Nurgak/Snail-Mail-Notifier/Images/emitter_etched.jpg

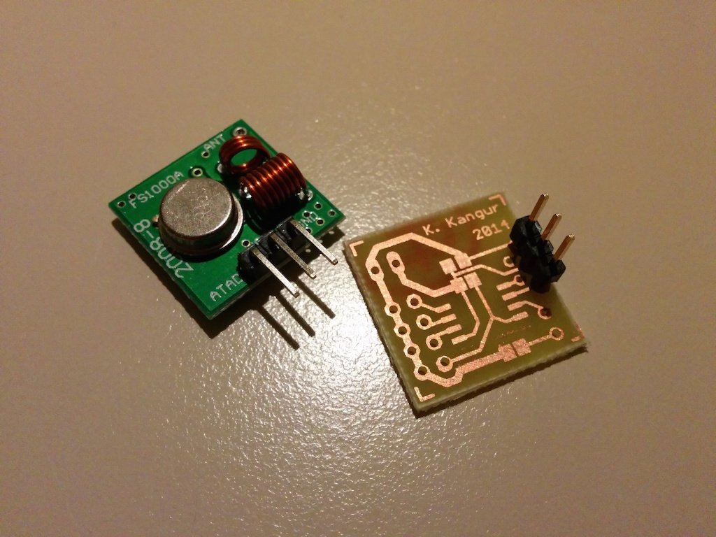
Images/emitter_etched.jpg
