Nurgak/Snail-Mail-Notifier/Images/emitter_programming.jpg

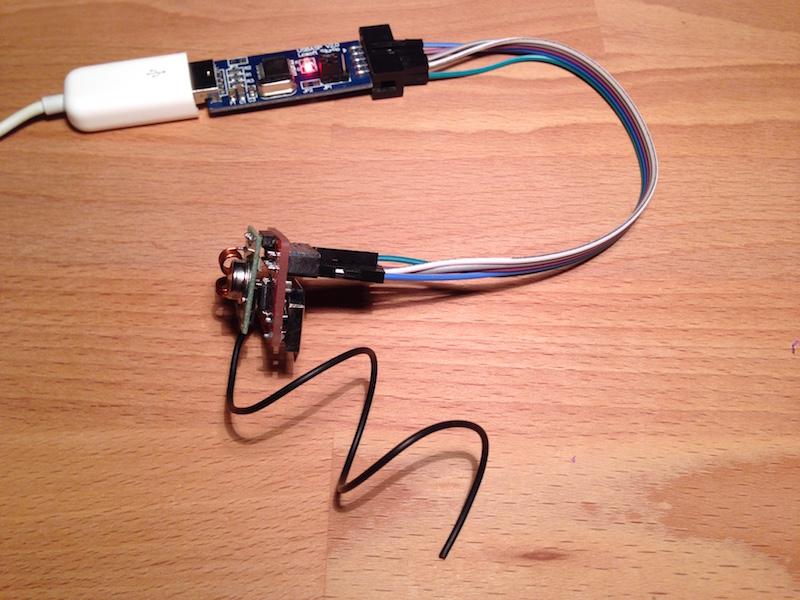
Images/emitter_programming.jpg
