Nurgak/Snail-Mail-Notifier/Images/media-20150113.jpg

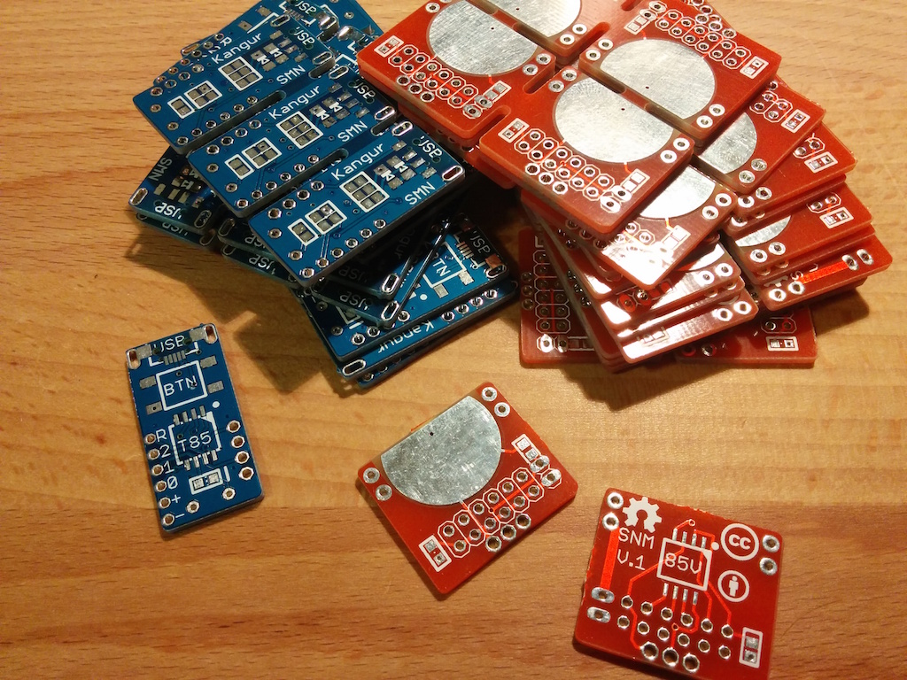
Images/media-20150113.jpg
