Nurgak/Snail-Mail-Notifier/Images/receiver.jpg

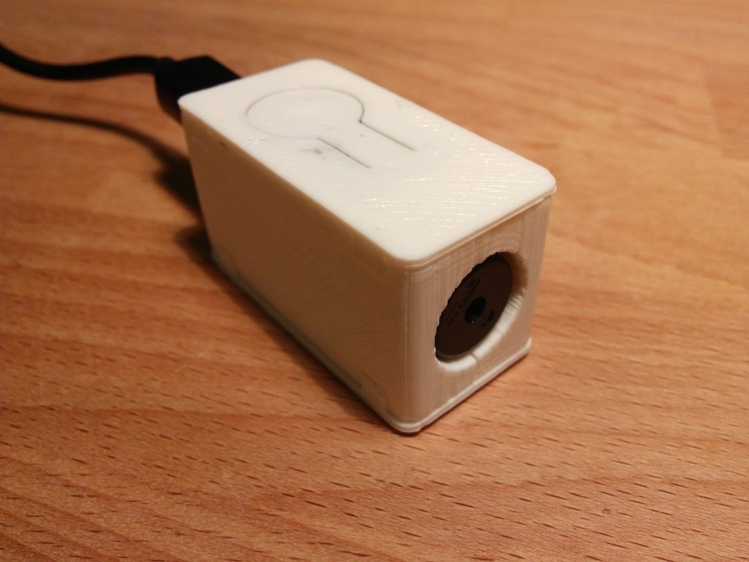
Images/receiver.jpg
