Nurgak/Snail-Mail-Notifier/Images/receiver_2.jpg

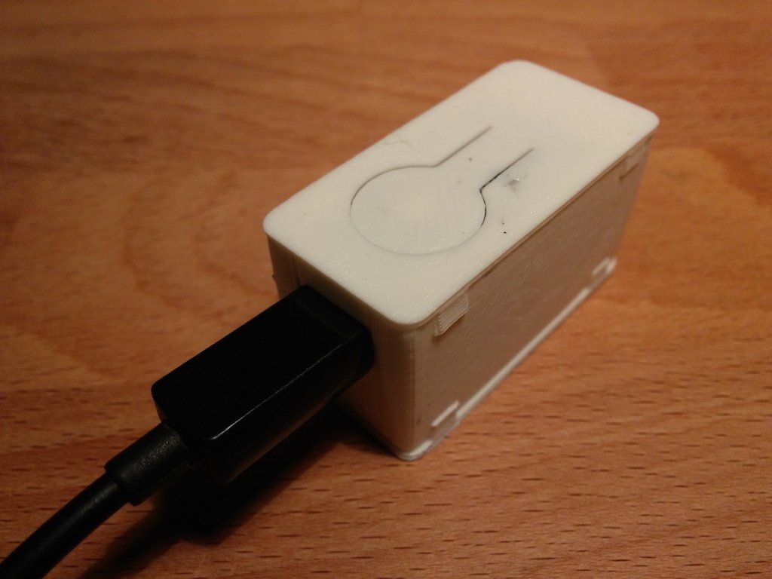
Images/receiver_2.jpg
