Nurgak/Snail-Mail-Notifier/Images/emitter_current_usage.jpg

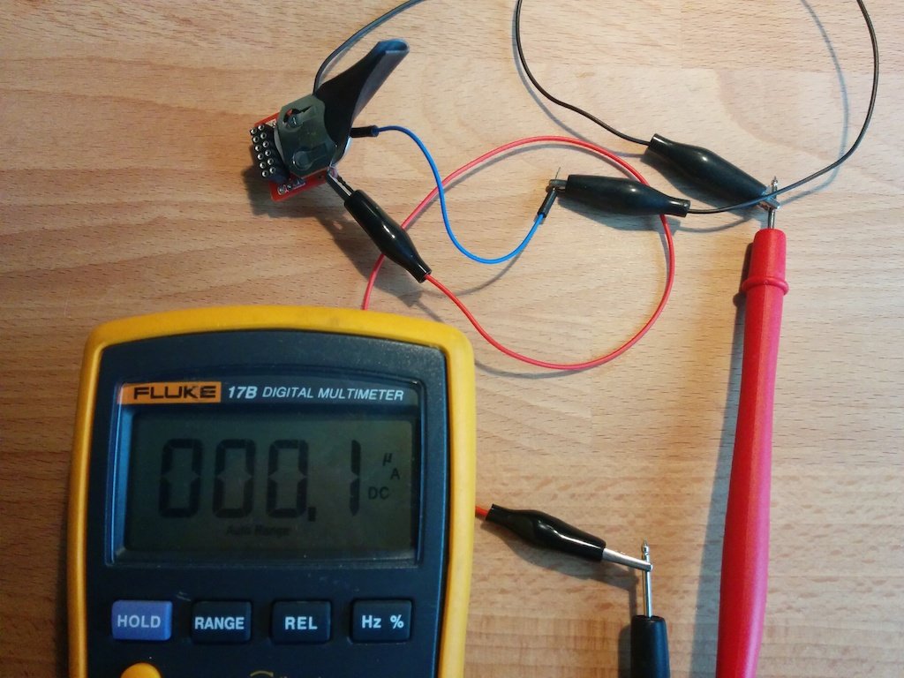
Images/emitter_current_usage.jpg
