Nurgak/Snail-Mail-Notifier/Images/emitter_etched_assembled.jpg

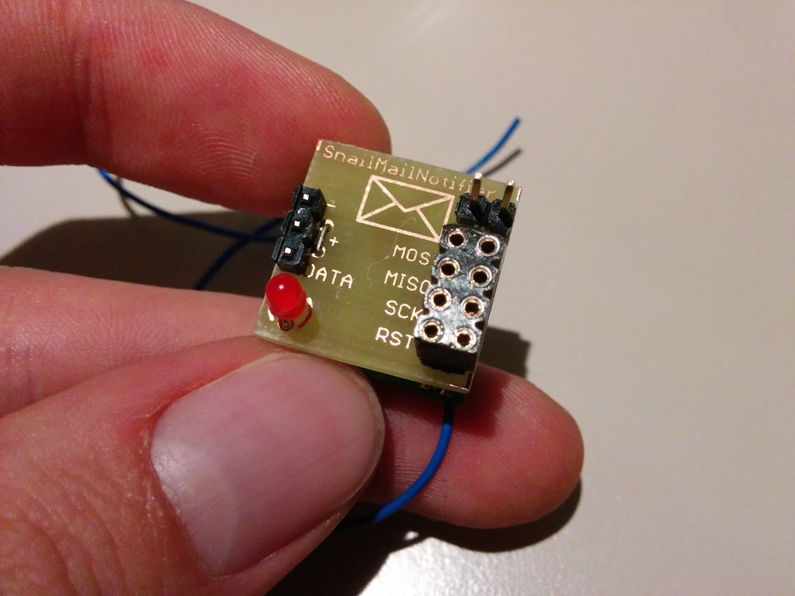
Images/emitter_etched_assembled.jpg
