Nurgak/Snail-Mail-Notifier/Images/receiver_current_measurement.jpg

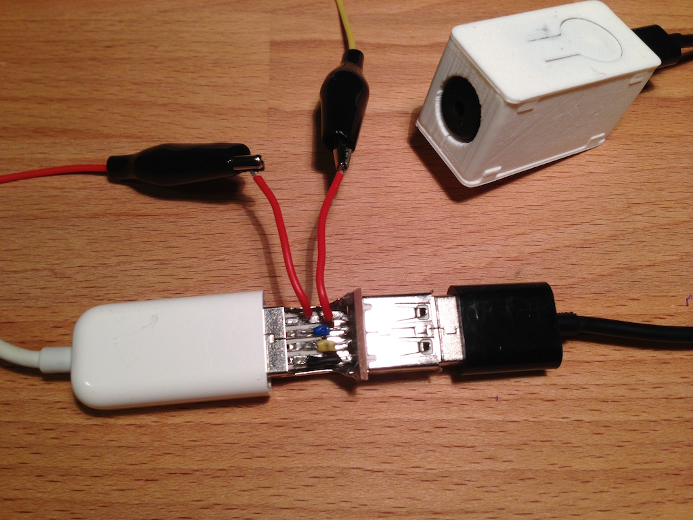
Images/receiver_current_measurement.jpg
