Nurgak/Snail-Mail-Notifier/Software/Arduino/SMN_Receiver/pitch.h

/***************************************************************************************
 *
 * Title:       Snail Mail Notifier - Receiver
 * File:        pitch.h
 * Version:     v0.1
 * Date:        2016-01-24
 * Author:      Karl Kangur <karl.kangur@gmail.com>
 * Licence:     CC-BY
 * Website:     https://github.com/Nurgak/Snail-Mail-Notifier
 * Development: https://hackaday.io/project/1954-snail-mail-notifier
 *
 ***************************************************************************************/
// Frequencies for equal-tempered scale, A4 = 440Hz
// Reference: http://www.phy.mtu.edu/~suits/notefreqs.html

#ifndef _pitch_h
#define _pitch_h

// Scientific name
#define C0  16
#define C0s 17
#define D0b 17
#define D0  18
#define D0s 19
#define E0b 19
#define E0  21
#define F0  22
#define F0s 23
#define G0b 23
#define G0  25
#define G0s 26
#define A0b 26
#define A0  28
#define A0s 29
#define B0b 29
#define B0  31
#define C1  33
#define C1s 35
#define D1b 35
#define D1  37
#define D1s 39
#define E1b 39
#define E1  41
#define F1  44
#define F1s 46
#define G1b 46
#define G1  49
#define G1s 52
#define A1b 52
#define A1  55
#define A1s 58
#define B1b 58
#define B1  62
#define C2  65
#define C2s 69
#define D2b 69
#define D2  73
#define D2s 78
#define E2b 78
#define E2  82
#define F2  87
#define F2s 93
#define G2b 93
#define G2  98
#define G2s 104
#define A2b 104
#define A2  110
#define A2s 117
#define B2b 117
#define B2  123
#define C3  131
#define C3s 139
#define D3b 139
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
#define P72 1661
#define P73 1760
#define P74 1865
#define P75 1976
#define P76 2093
#define P77 2217
#define P78 2349
#define P79 2489
#define P80 2637
#define P81 2794
#define P82 2960
#define P83 3136
#define P84 3322
#define P85 3520
#define P86 3729
#define P87 3951
#define P88 4186

#endif
